songch9511/zen-cad/skills/cad-handoff/references/runtime-contract.md

# Runtime Contract

Read this when a downstream CAD generator, viewer, or inspector has its own commands, geometry reference syntax, or artifact conventions.

## Rule

Core Zen CAD specs stay kernel-neutral. Tool-specific commands belong in adapter references or handoff prompts.

## Adapter Mapping

An adapter prompt should map Zen CAD concepts to the active harness:

- CAD source generation;
- optional kernel-neutral layout proxy scene generation;
- optional locked-facts inspection of a layout proxy scene;
- optional CAD source export and source-level inspection;
- optional build123d source execution, STEP export, STEP re-import, and basic geometry inspection;
- optional feature-plan carry-through for holes, bores, repeated patterns, rectangular chamfers, simplified gear teeth, and supported edge-round approximations;
- optional local viewer link packaging for generated STEP artifacts;
- proceed-gate package generation;
- proceed approval recording;
- detail-upgrade handoff generation from a matching approval artifact;
- approved text-to-cad prompt bundle packaging;
- explicit primary artifact path;
- generated files as derived artifacts;
- source/spec as the source of truth;
- harness-native geometry references;
- deterministic inspection commands;
- visual review or snapshot commands;
- viewer handoff;
- skipped-check reporting;
- smallest source-level repair and rerun policy.
- explicit no-generation boundary when the adapter only packages a downstream prompt.

Do not pretend the build123d vertical slice is a full CADSkills-equivalent runtime. If the active harness lacks a check, state the missing capability and keep the limitation visible. Viewer links are review aids; geometry checks and locked-fact carry-through remain the stronger evidence.
